home-suite-home/Home-Suite-Home/analytics/command_response_1615932081.png

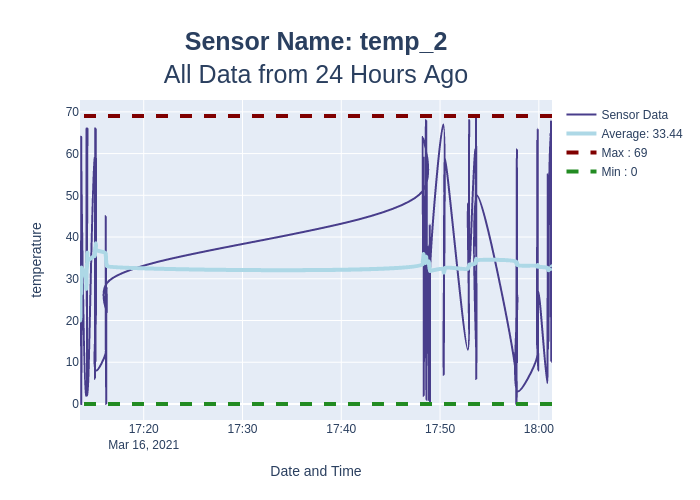
analytics/command_response_1615932081.png
