home-suite-home/Home-Suite-Home/analytics/command_response_1616091843.png

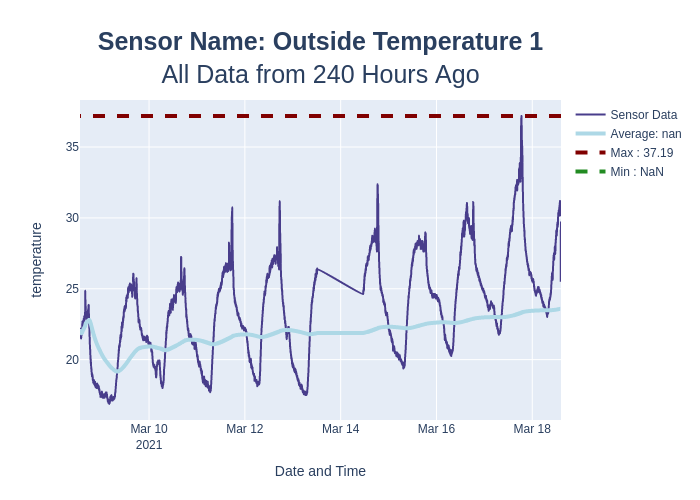
analytics/command_response_1616091843.png
