home-suite-home/Home-Suite-Home/analytics/command_response_1616092217.png

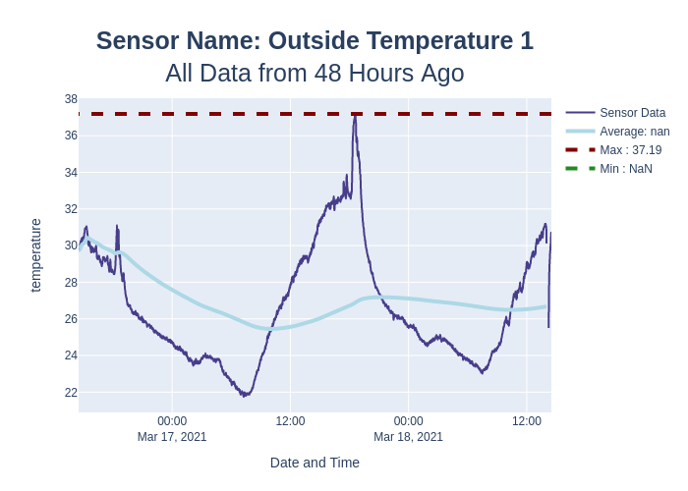
analytics/command_response_1616092217.png
