home-suite-home/Home-Suite-Home/artifacts/assets/mongodb_stats_stess.png

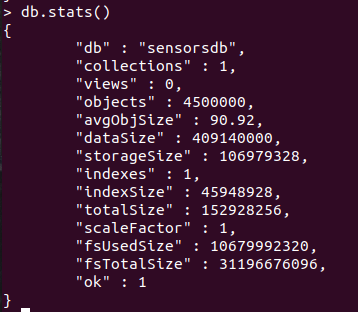
artifacts/assets/mongodb_stats_stess.png
