home-suite-home/Home-Suite-Home/artifacts/assets/screenshot_email_ui.png

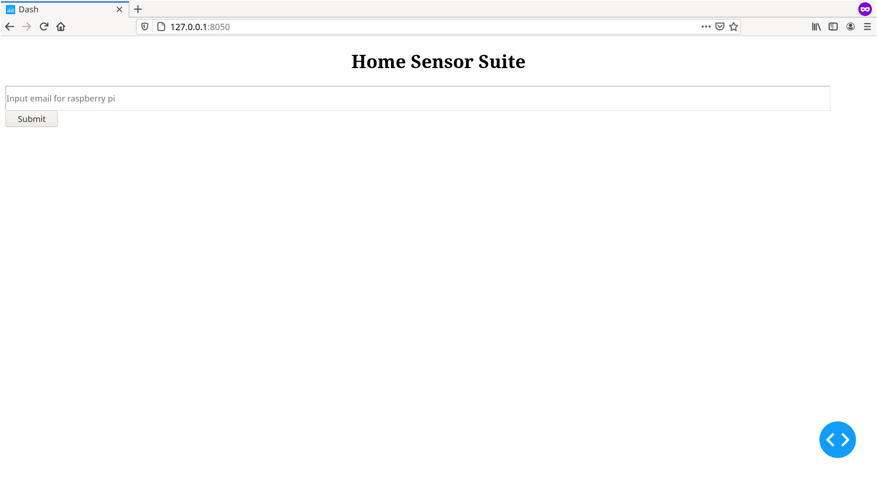
artifacts/assets/screenshot_email_ui.png
