home-suite-home/Home-Suite-Home/source/analytics/command_response_1616629806.png

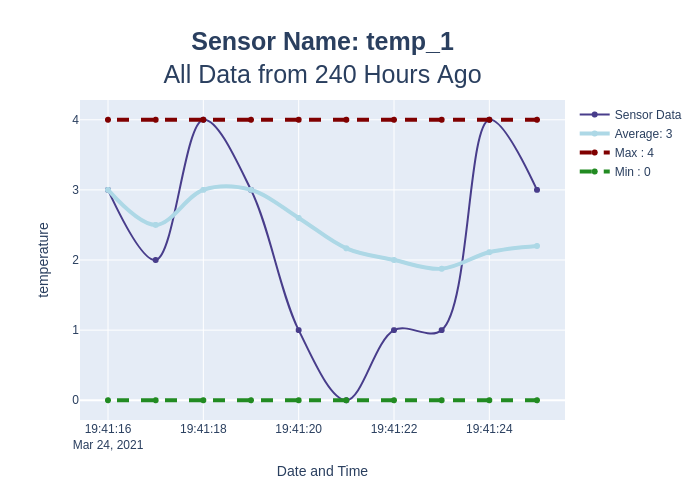
source/analytics/command_response_1616629806.png
