home-suite-home/Home-Suite-Home/sensor_source/temperature_probe/config.h

#ifndef config_h
#define config_h

#include "Arduino.h"

const char NETWORK_NAME[] = "YOUR_NETWORK_NAME";
const char NETWORK_PASSWORD[] = "YOUR_NETWORK_PASSWORD";

// Deprecated feature below left in for ranges - will remove for production release

// dry value is in range 15 - 25
// one small drop is in range 40 - 110
// submerged maximum value is 420
// const int SENSITIVITY = 40;

#endif
